TU-DO-Makerspace/DEPRECATED_TU-DO-Dimmer/src/PatchIndicator.h

  /*
   * Copyright (C) 2020  Patrick Pedersen, The TU-DO Makespace

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
   * Author: Patrick Pedersen <ctx.xda@gmail.com>
   * Description: A hardware abstraction class for the 7-segment patch indicator
   * 
   */

#pragma once

#include <stdint.h>

#define COMMON_ANODE 0
#define COMMON_CATHODE 1

/*
 * PatchIndicator
 * --------------
 * Description:
 *      A driver class for the 7-segment patch indicator display.
 *      This class can display a digit for a given duration using the display() function,
 *      as well as flash a digit n times for a given duration, using the display() function.
 */

class PatchIndicator
{
        // Segments for digits 0 - 9
        bool digits[10][7] {
                // 0
                {
                        true, true, true, true, true, true, false
                },
                // 1
                {
                        false, true, true, false, false, false, false
                },
                // 2
                {
                        true, true, false, true, true, false, true
                },
                // 3
                {
                        true, true, true, true, false, false, true
                },
                // 4
                {
                        false, true, true, false, false, true, true
                },
                // 5
                {
                        true, false, true, true, false, true, true
                },
                // 6
                {
                        true, false, true, true , true, true, true
                },
                // 7
                {
                        true, true, true, false, false, false, false
                },
                // 8
                {
                        true, true, true, true, true, true, true
                },
                // 9
                {
                        true, true, true, true, false, true, true
                }
        };

        bool _state;                    // True if display is on, false if off
        bool _config;                   // Stores whether the 7 segment display is a common anode(0) or common cathode(1) display
        uint8_t _common;                // Pin of common anode or cathode
        uint8_t _segments[7];           // Pins of all segments (a to g)

        bool _busy = false;             // True if patch indicator is scheduled

        bool _show = false;             // True if patch indicator is tasked to display a number
        unsigned long _show_tstamp;     // Timestamp for displaying digits


        uint8_t _blinks;                                       // Number of blinks the patch indicator should perform
        unsigned long _blink_interval_on, _blink_interval_off; // Duration of on and off intervals for blinks
        unsigned long _blink_tstamp;                           // Timestamp for blink intervals

        void select(bool select);
        void toggle();

public:
        PatchIndicator();
        PatchIndicator(bool config, uint8_t common, uint8_t a, uint8_t b, uint8_t c, uint8_t d, uint8_t e, uint8_t f, uint8_t g, uint8_t dp);

        void set(uint8_t num);
        bool busy();
        void update();
        void blink(uint8_t blinks, unsigned long interval_on, unsigned long interval_off);
        void show(unsigned long duration);
};
