TU-DO-Makerspace/DEPRECATED_TU-DO-Dimmer/src/credits.cpp

  /*
   * Copyright (C) 2020  Patrick Pedersen, The TU-DO Makespace

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
   * Author: Patrick Pedersen <ctx.xda@gmail.com>
   * Description: Authors credit ;)
   * 
   */

#include "config.h"
#include "credits.h"

/*
 * flash
 * -----------
 * Parameters:
 *      rgbstrp - Pointer to a NeoPixel RGB strip driver object
 *      color - Color to be flashed
 *      duration - Duration for color to be flashed 
 * Description:
 *      "Flashes"/Displays a provided color for a provided duration.
 *      The RGB strip must still be turned off manually after this function
 *      has been called.
 */

void flash(RGBStrip *rgbstrp, RgbColor color, unsigned long duration)
{
        rgbstrp->set(color);
        delay(duration);
}

/*
 * flash
 * -----------
 * Parameters:
 *      rgbstrp - Pointer to a NeoPixel RGB strip driver object
 * Description:
 *      Author credits
 */

void authors_credit(RGBStrip *rgbstrp)
{
        RgbColor off(0, 0, 0);
        RgbColor red(255, 0, 0);
        RgbColor green(0, 0, 255);
        RgbColor blue(0, 255, 0);
        RgbColor white(255, 255, 255);

        flash(rgbstrp, RgbColor(0, 0, 0), 1000);

        // C
        flash(rgbstrp, red, MORSE_LONG);
        flash(rgbstrp, off, MORSE_BTWN);
        flash(rgbstrp, red, MORSE_SHORT);     
        flash(rgbstrp, off, MORSE_BTWN);
        flash(rgbstrp, red, MORSE_LONG);
        flash(rgbstrp, off, MORSE_BTWN);
        flash(rgbstrp, red, MORSE_SHORT);

        flash(rgbstrp, off, MORSE_LETTER);

        // T
        flash(rgbstrp, green, MORSE_LONG);

        flash(rgbstrp, off, MORSE_LETTER);

        // X
        flash(rgbstrp, off, MORSE_LONG);
        flash(rgbstrp, off, MORSE_BTWN);
        flash(rgbstrp, blue, MORSE_SHORT);     
        flash(rgbstrp, off, MORSE_BTWN);
        flash(rgbstrp, blue, MORSE_SHORT);     
        flash(rgbstrp, off, MORSE_BTWN);

        // z
        flash(rgbstrp, off, MORSE_LONG);
        flash(rgbstrp, off, MORSE_BTWN);
        flash(rgbstrp, white, MORSE_SHORT);     
        flash(rgbstrp, off, MORSE_BTWN);
        flash(rgbstrp, white, MORSE_SHORT);     
        flash(rgbstrp, off, MORSE_BTWN);

        flash(rgbstrp, RgbColor(0, 0, 0), 1000);
}
